PyroProtato/pinecil-case/Hinge Test/3dp/innerhinge2.stp

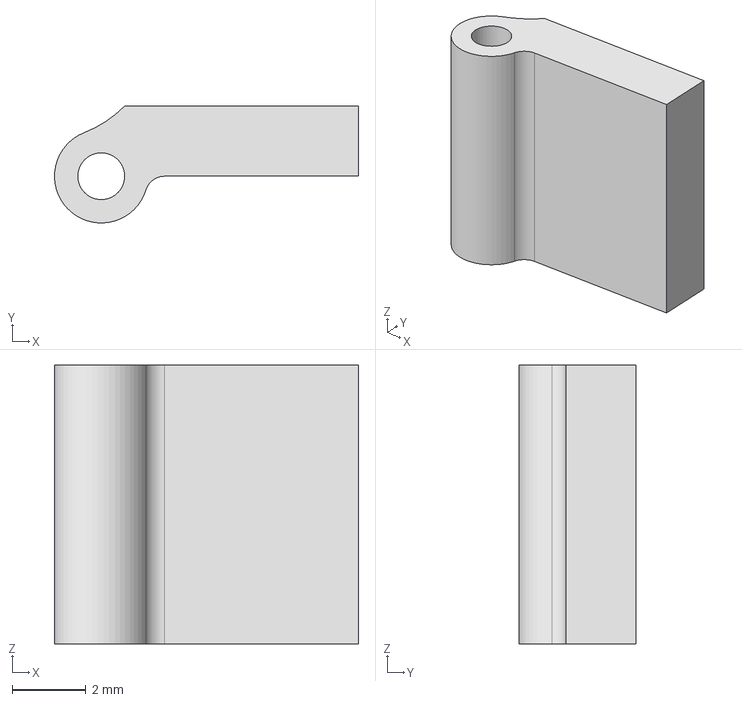
[picture p15: CAD file, 2025-10-13]
Hinge Test/3dp/innerhinge2.stp
8.25 x 3.17 x 7.57 mm
