PyroProtato/pinecil-case/3D Print Tests/Pinecil Clip.stp

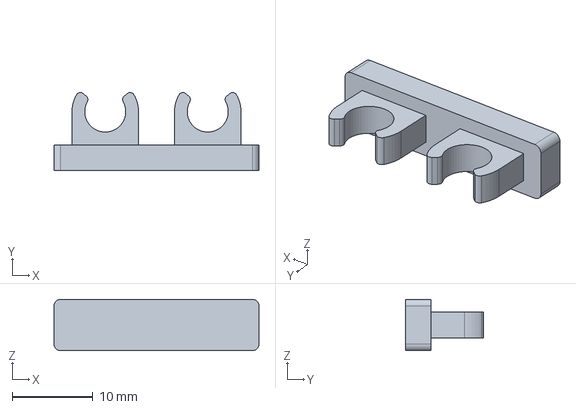
[picture p16: CAD file, 2025-10-13]
3D Print Tests/Pinecil Clip.stp
25.4 x 9.67 x 6.35 mm
