PyroProtato/pinecil-case/3D Print Tests/Pinecil ClipV3.stp

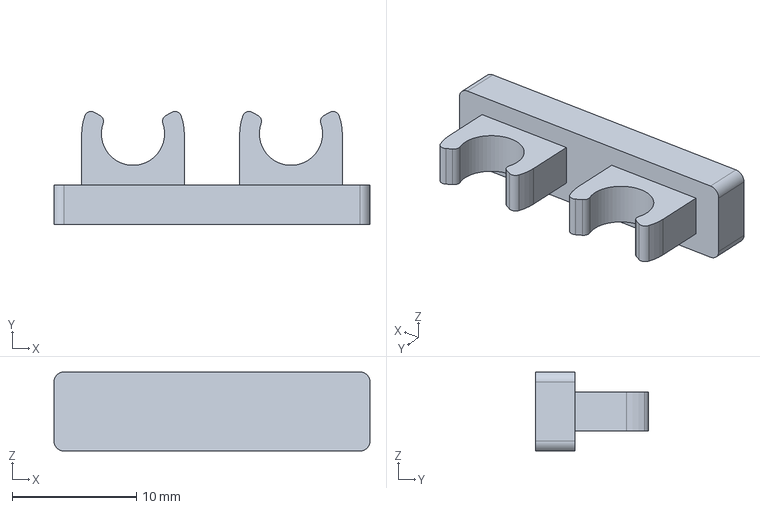
[picture p17: CAD file, 2025-10-13, an earlier design]
3D Print Tests/Pinecil ClipV3.stp
25.4 x 9.09 x 6.35 mm
