PyroProtato/pinecil-case/3D Print Tests/Pinecil Clip V4.stp

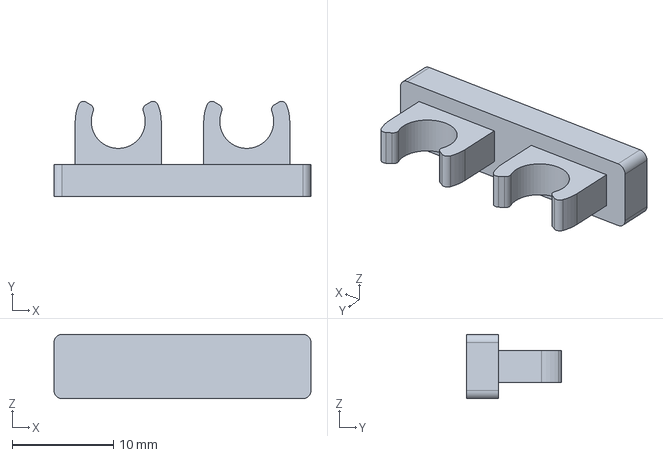
[picture p18: CAD file, 2025-10-13, an earlier design]
3D Print Tests/Pinecil Clip V4.stp
25.4 x 9.40 x 6.35 mm
